nostradomus/atmega88-168-328_programmer_shield/images/copper side - right 3D perspective.png

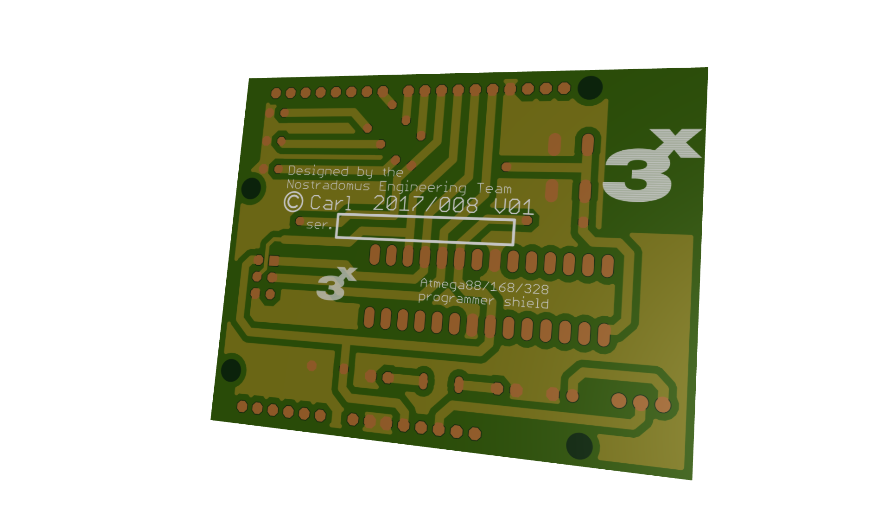
images/copper side - right 3D perspective.png
