nostradomus/atmega88-168-328_programmer_shield/images/copper_side-frontal_view.png

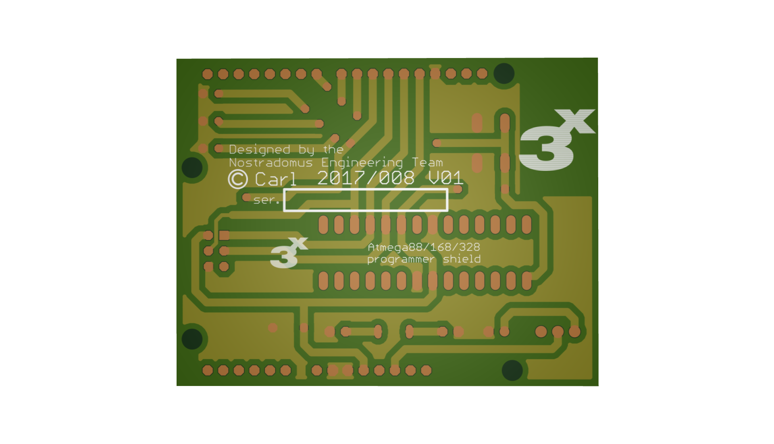
images/copper_side-frontal_view.png
