nostradomus/atmega88-168-328_programmer_shield/images/copper_side-left_3D_perspective.png

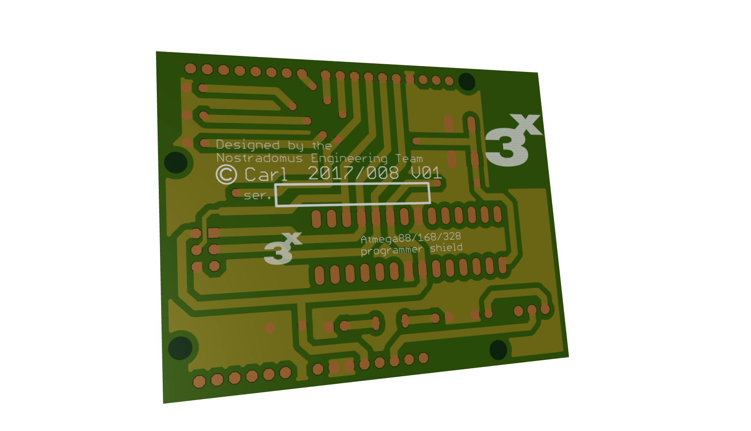
images/copper_side-left_3D_perspective.png
