nostradomus/atmega88-168-328_programmer_shield/images/minimal-version/copper side - right 3D perspective.png

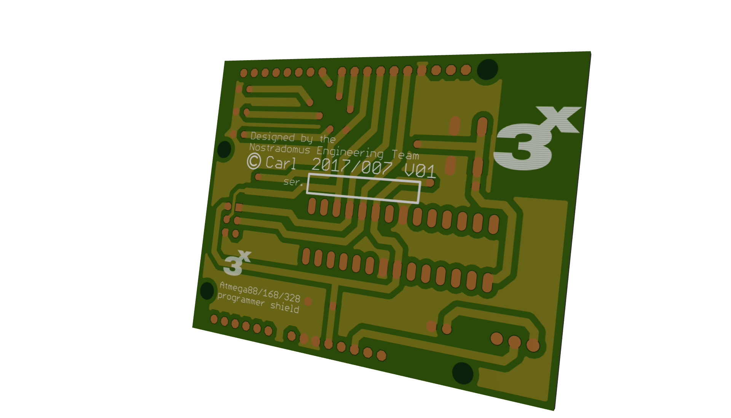
images/minimal-version/copper side - right 3D perspective.png
