nostradomus/atmega88-168-328_programmer_shield/images/minimal-version/copper_side-frontal_view-s.png

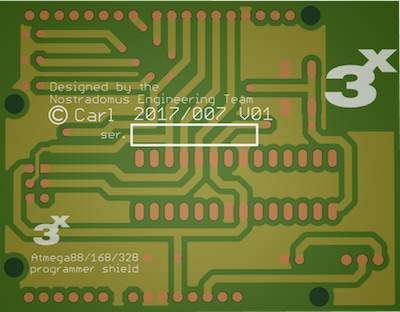
images/minimal-version/copper_side-frontal_view-s.png
