nostradomus/atmega88-168-328_programmer_shield/images/minimal-version/copper_side-left_3D_perspective-s.png

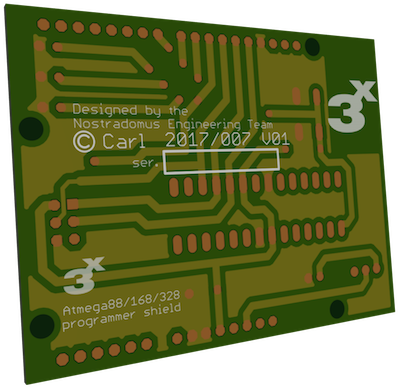
images/minimal-version/copper_side-left_3D_perspective-s.png
