nostradomus/atmega88-168-328_programmer_shield/images/minimal-version/pcb (no pour).png

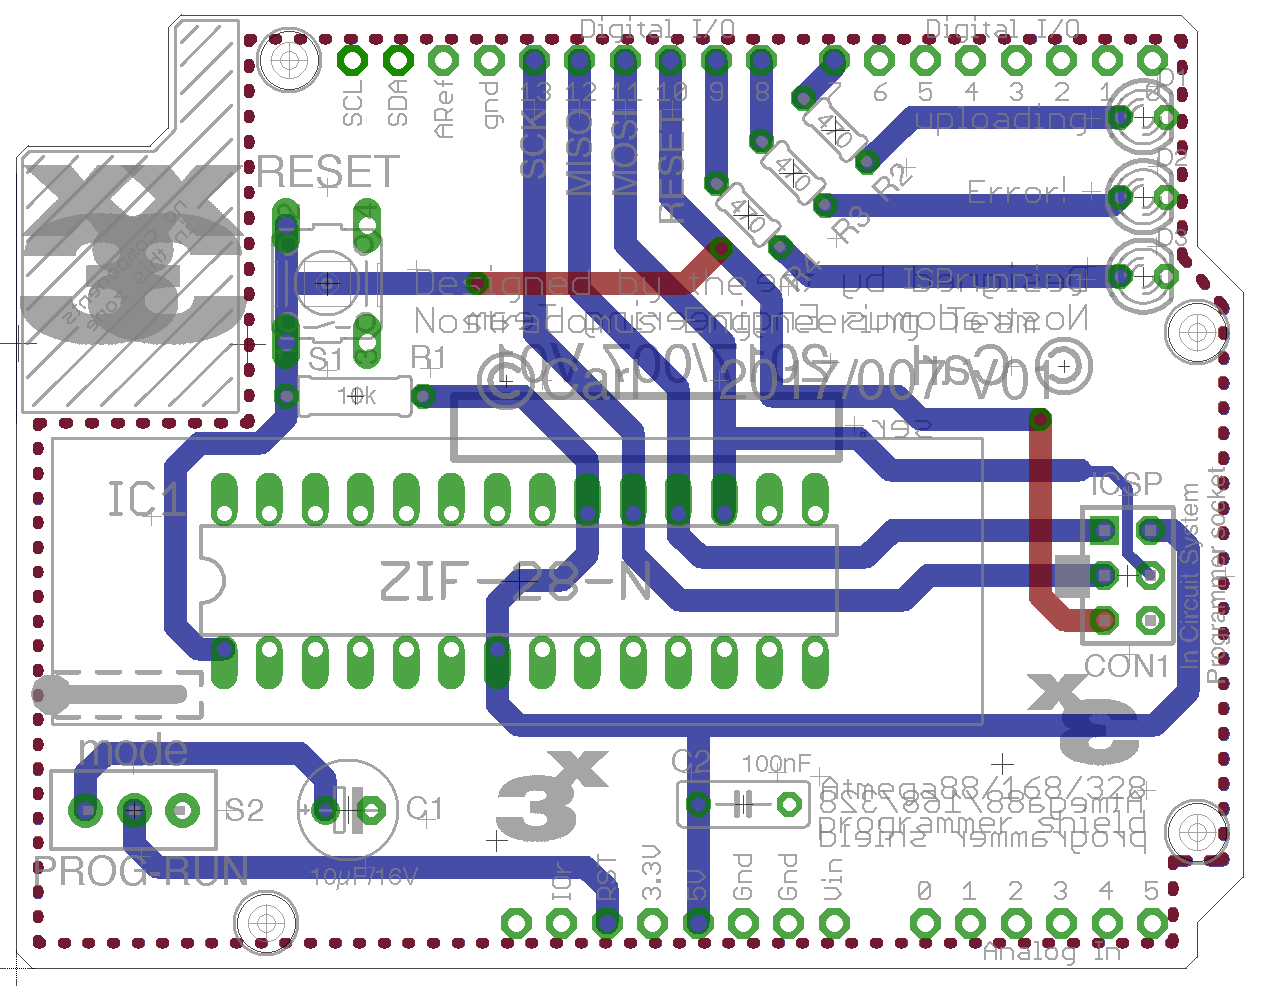
images/minimal-version/pcb (no pour).png
