nostradomus/atmega88-168-328_programmer_shield/images/minimal-version/pcb.png

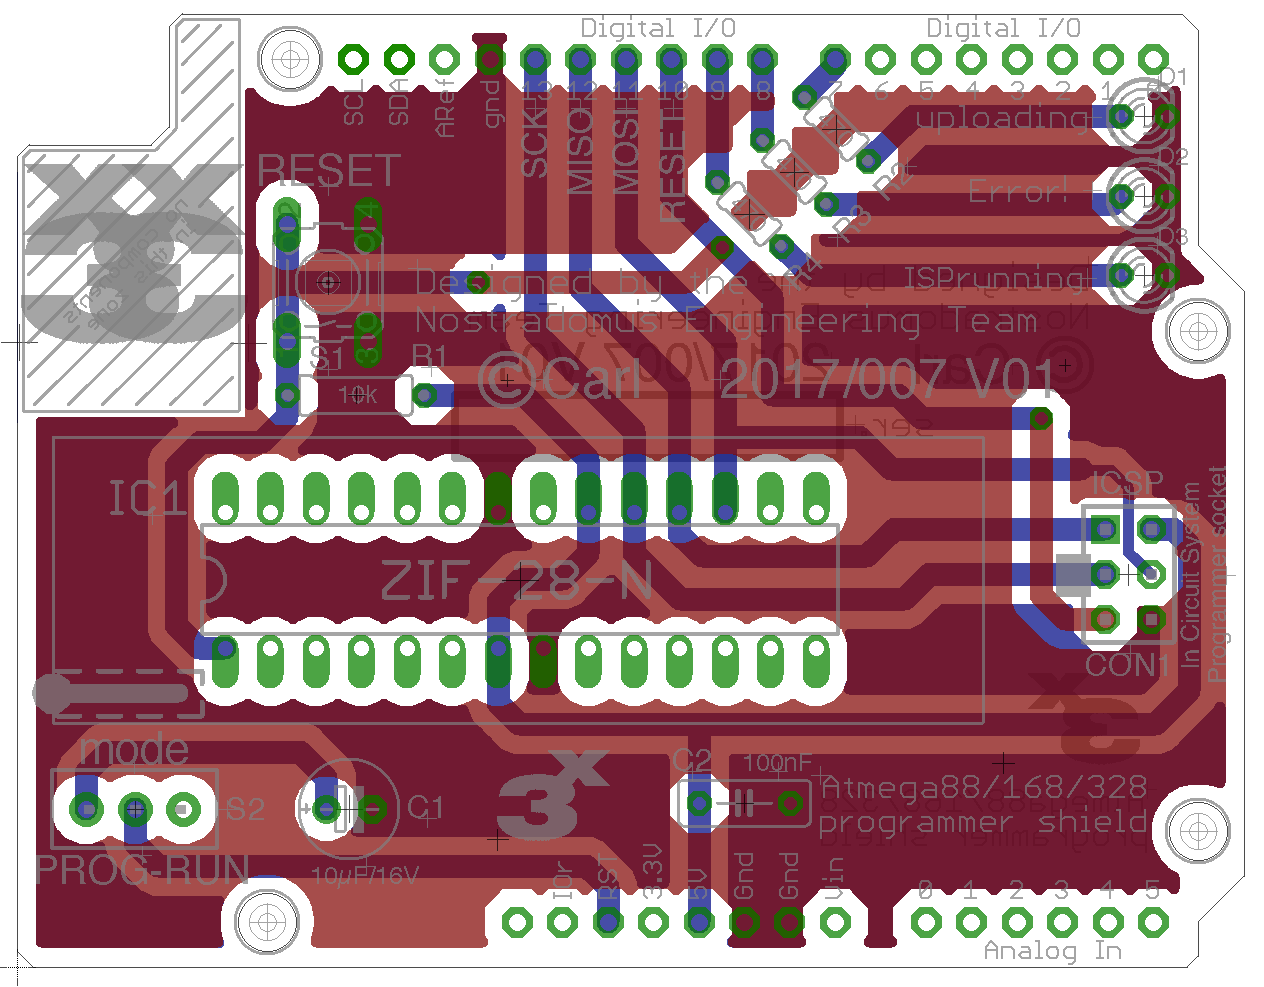
images/minimal-version/pcb.png
