nostradomus/atmega88-168-328_programmer_shield/images/minimal-version/schematic-s.png

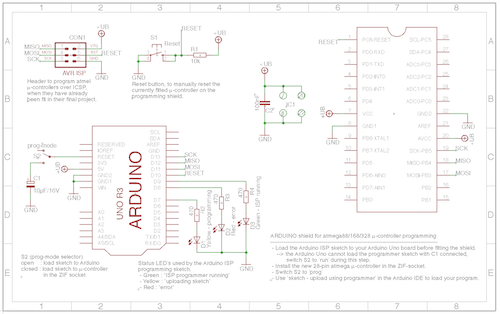
images/minimal-version/schematic-s.png
