nostradomus/atmega88-168-328_programmer_shield/images/minimal-version/shield (8MHz internal clock version).png

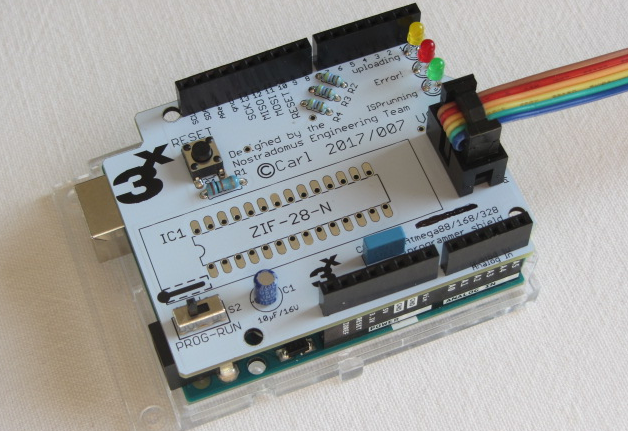
images/minimal-version/shield (8MHz internal clock version).png
