nostradomus/atmega88-168-328_programmer_shield/images/pcb (no pour).png

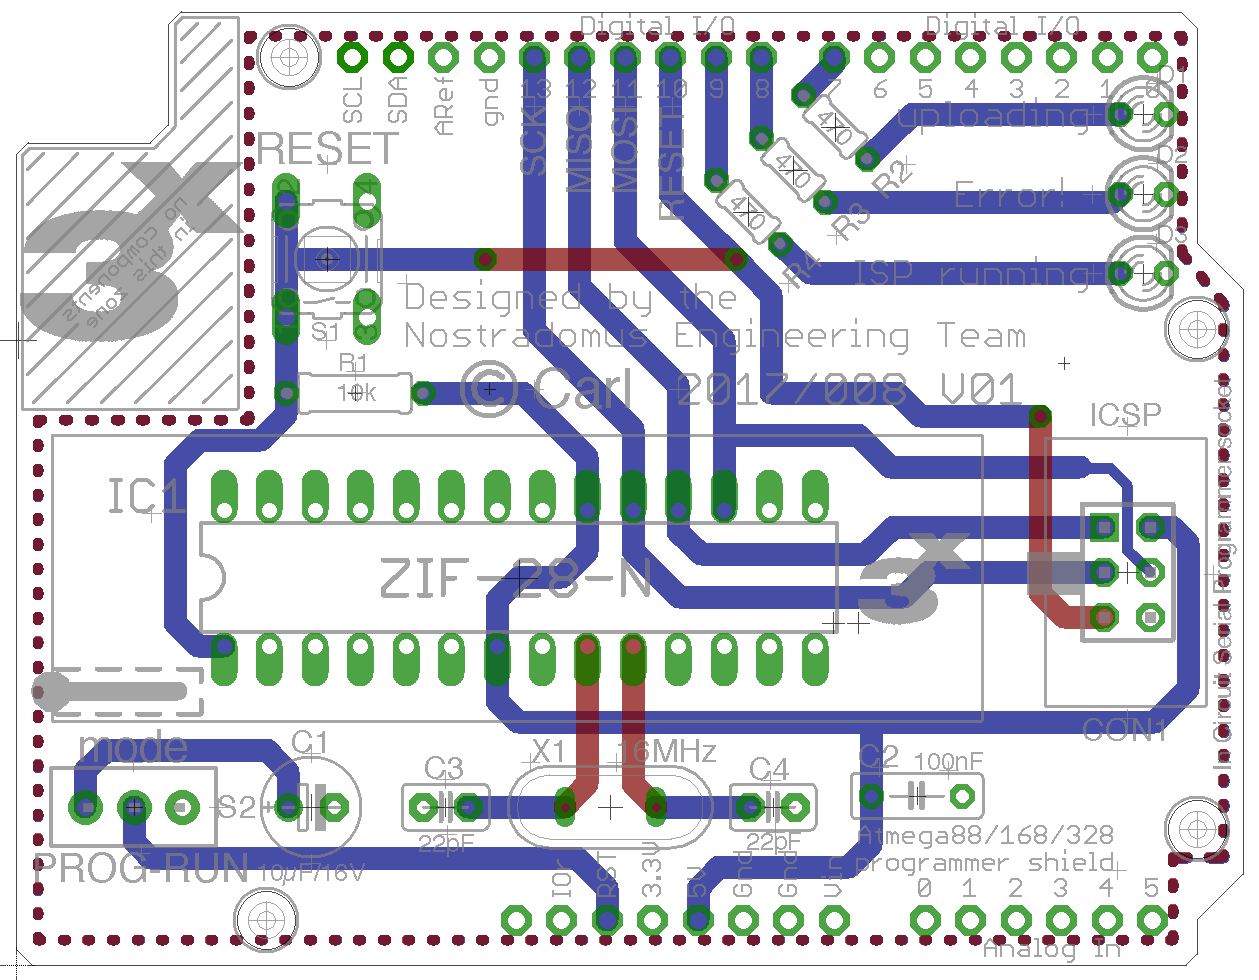
images/pcb (no pour).png
