nostradomus/atmega88-168-328_programmer_shield/images/component_side-right_3D_perspective.png

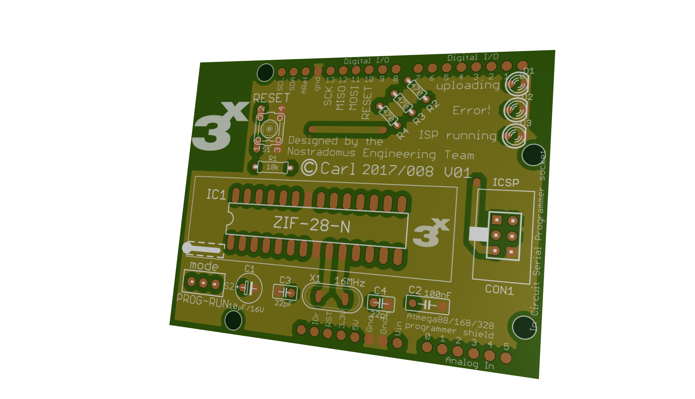
images/component_side-right_3D_perspective.png
