nostradomus/atmega88-168-328_programmer_shield/images/minimal-version/component side - left 3D perspective.png

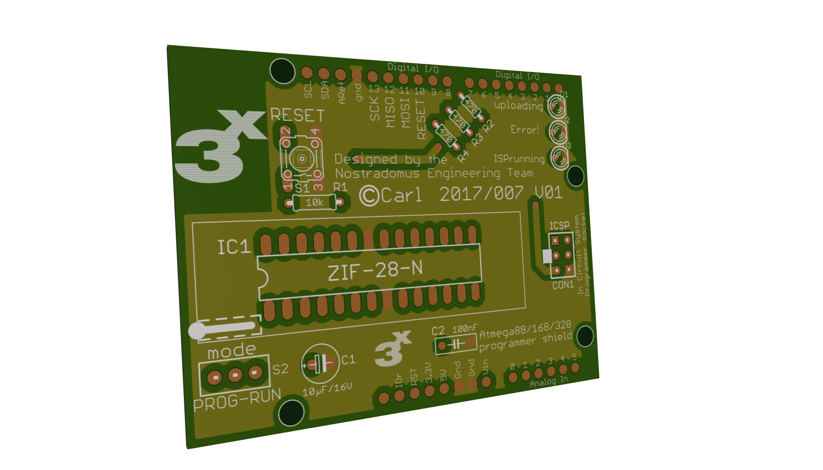
images/minimal-version/component side - left 3D perspective.png
