nostradomus/atmega88-168-328_programmer_shield/images/minimal-version/component_layout-s.png

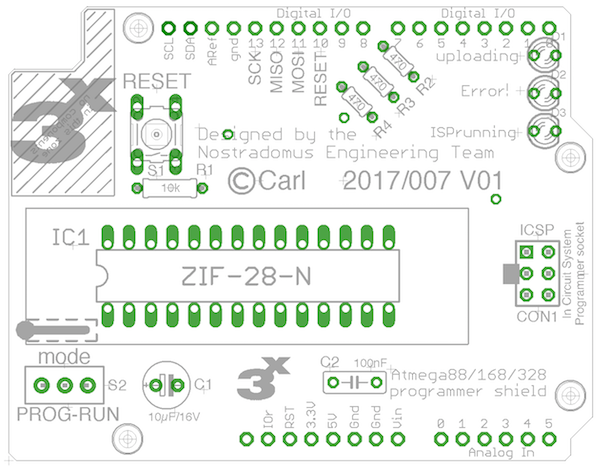
images/minimal-version/component_layout-s.png
