nostradomus/atmega88-168-328_programmer_shield/images/minimal-version/component_side-right_3D_perspective.png

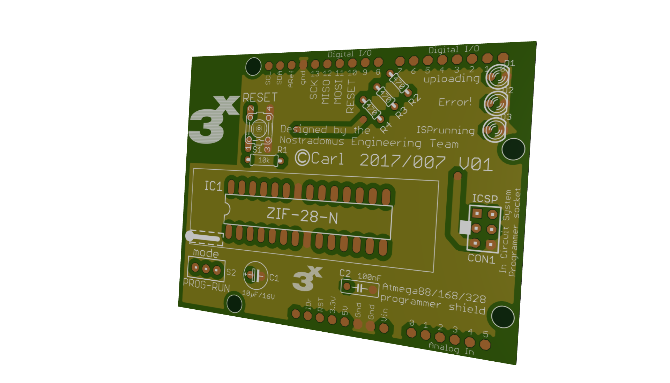
images/minimal-version/component_side-right_3D_perspective.png
