nostradomus/atmega88-168-328_programmer_shield/pdf-files/minimal-version/pcb.pdf

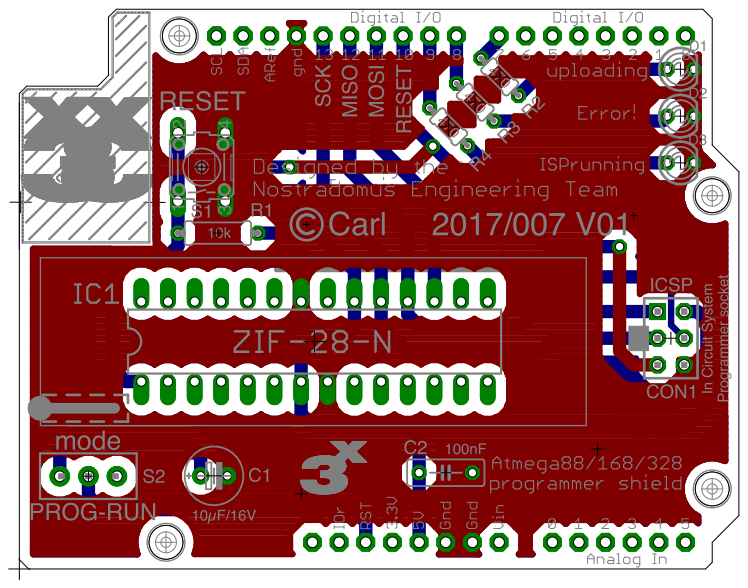
[picture p49: page 1]
